FESdevice2024/Functional_Electronic_Stimulation/FES Paper Images/Figure 5 Fab.png

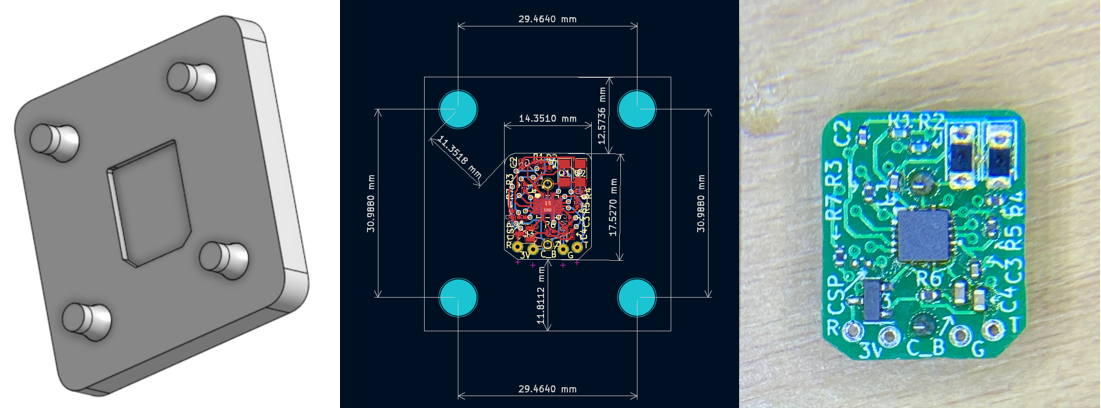
FES Paper Images/Figure 5 Fab.png
