FESdevice2024/Functional_Electronic_Stimulation/FES Paper Images/Figure 3 Battery Discharging For Clock.png

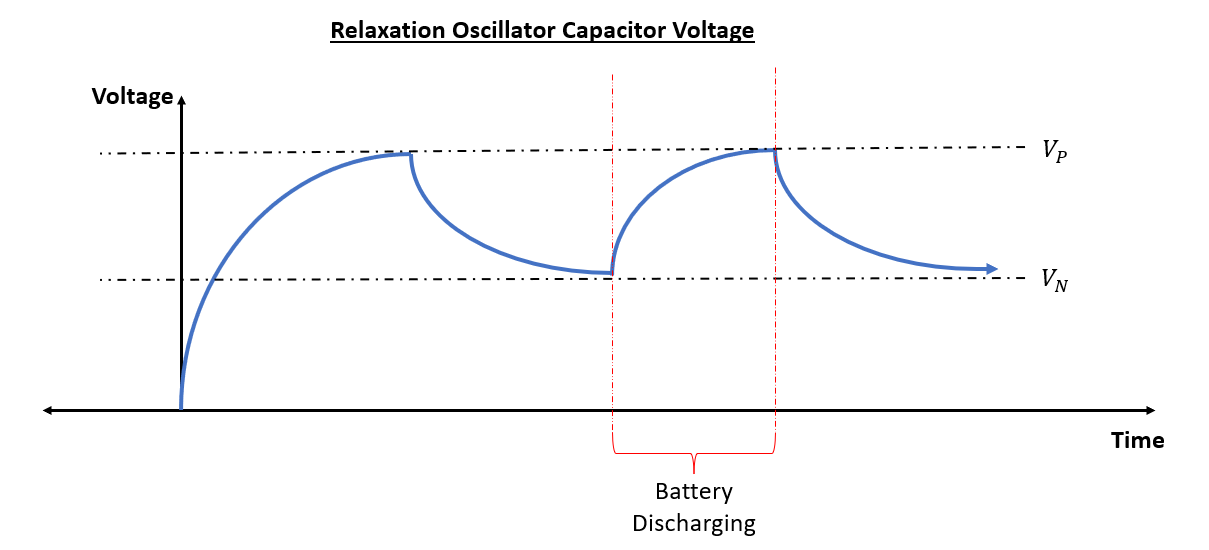
FES Paper Images/Figure 3 Battery Discharging For Clock.png
