FESdevice2024/Functional_Electronic_Stimulation/FES Paper Images/Figure 3 Cap Charging for Batt Life Calcs.png

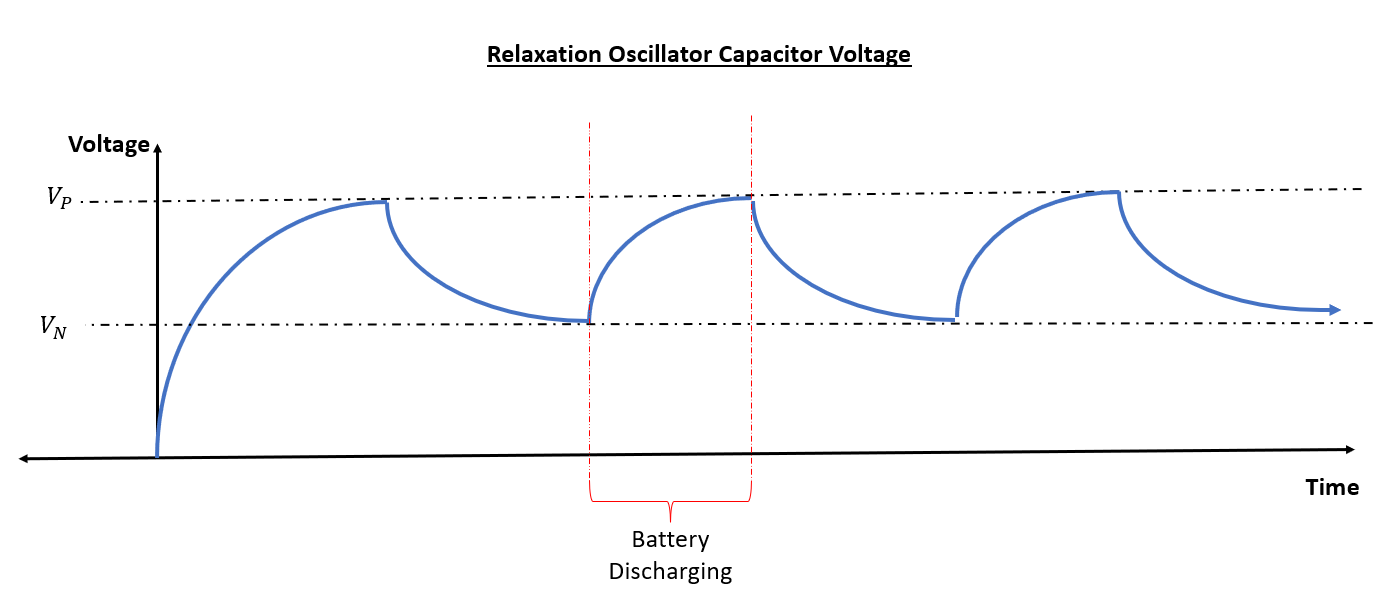
FES Paper Images/Figure 3 Cap Charging for Batt Life Calcs.png
