FESdevice2024/Functional_Electronic_Stimulation/FES Paper Images/Figure 7 Meas Hz.png

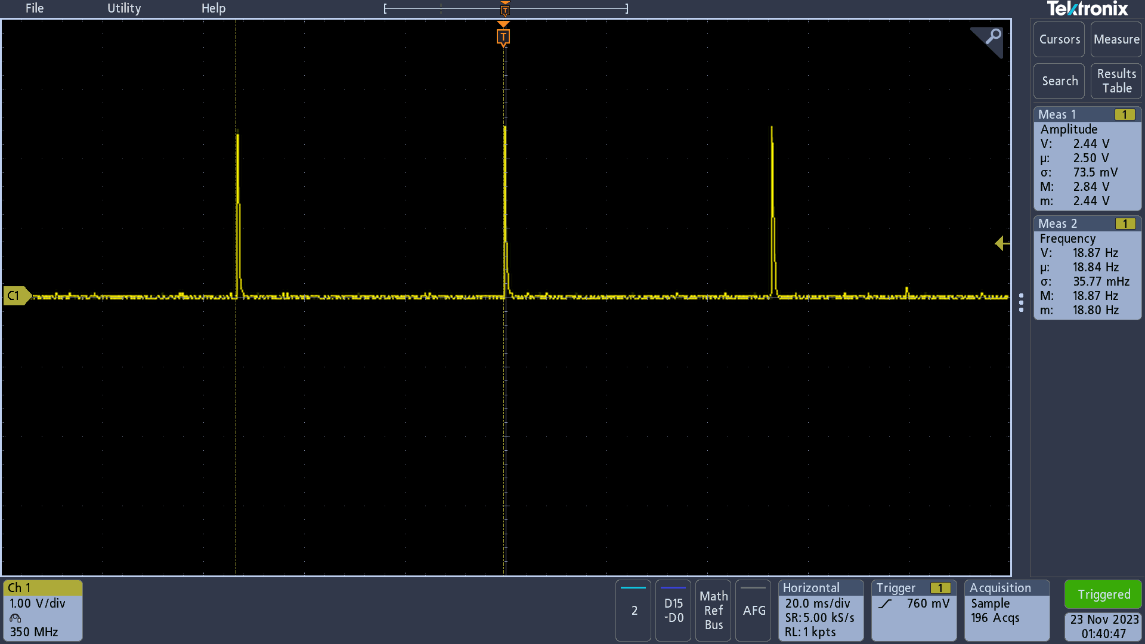
FES Paper Images/Figure 7 Meas Hz.png
