FESdevice2024/Functional_Electronic_Stimulation/FES Paper Images/Figure 8 Pulse Width.png

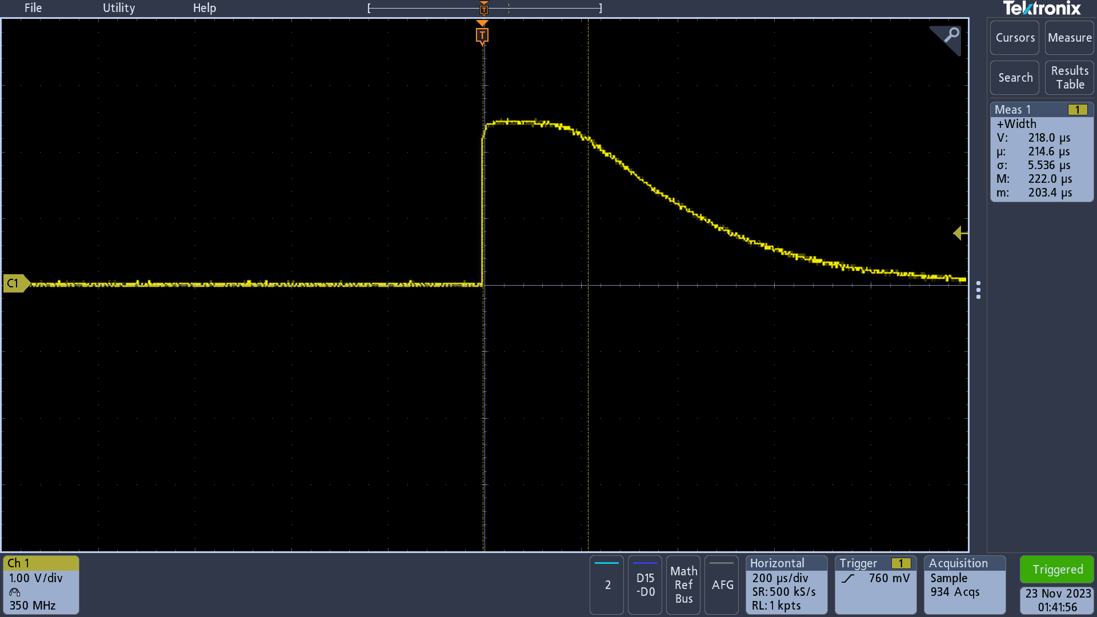
FES Paper Images/Figure 8 Pulse Width.png
