FESdevice2024/Functional_Electronic_Stimulation/FES Paper Images/Salmons Original Circuit Figure 1.jpg

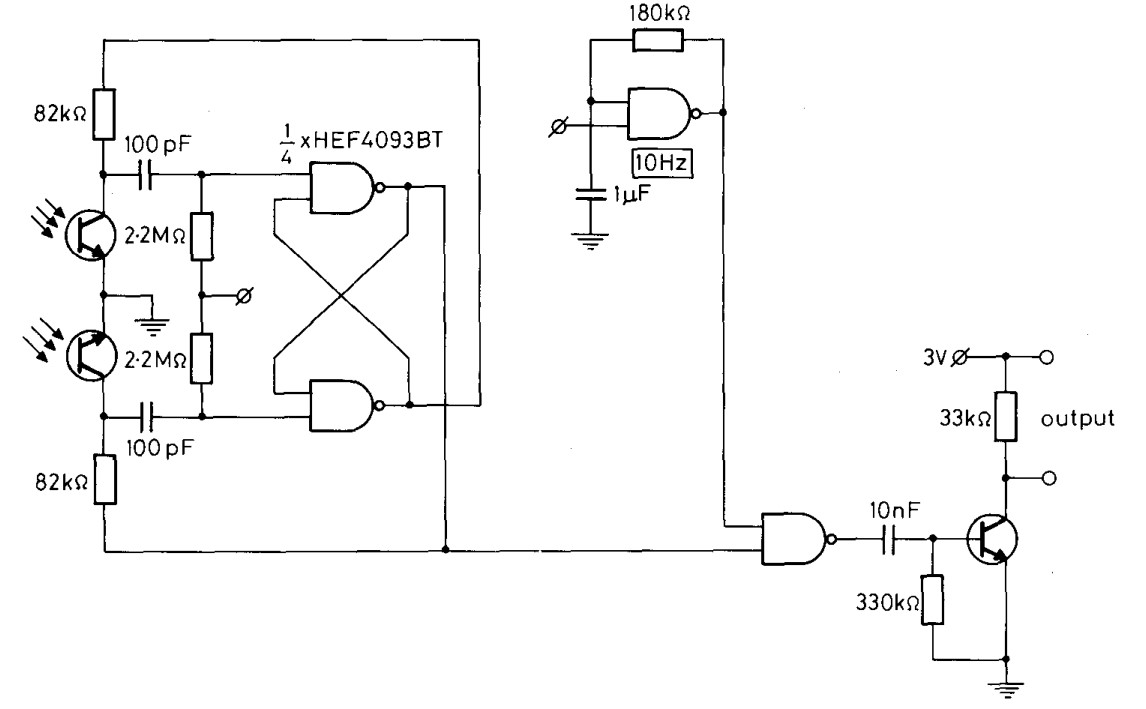
FES Paper Images/Salmons Original Circuit Figure 1.jpg
