FESdevice2024/Functional_Electronic_Stimulation/FES Oscilloscope Images From Testing/clock1.png

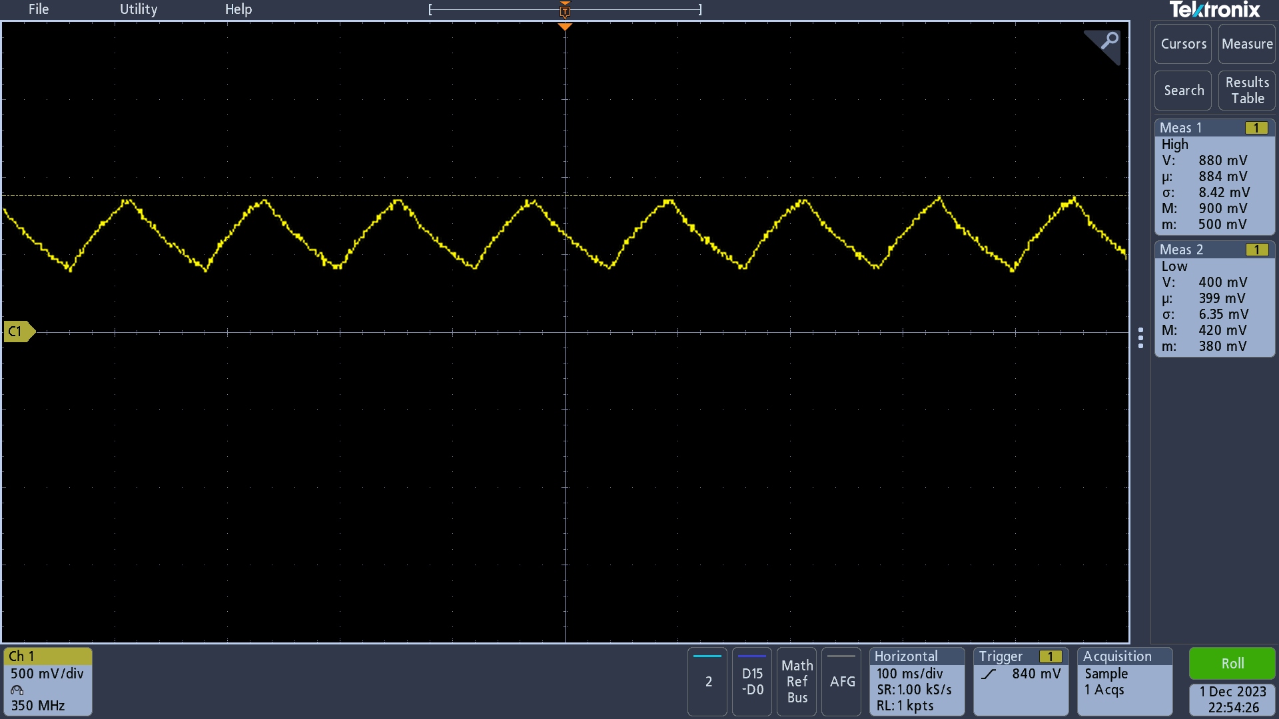
FES Oscilloscope Images From Testing/clock1.png
