FESdevice2024/Functional_Electronic_Stimulation/FES Oscilloscope Images From Testing/clock5.png

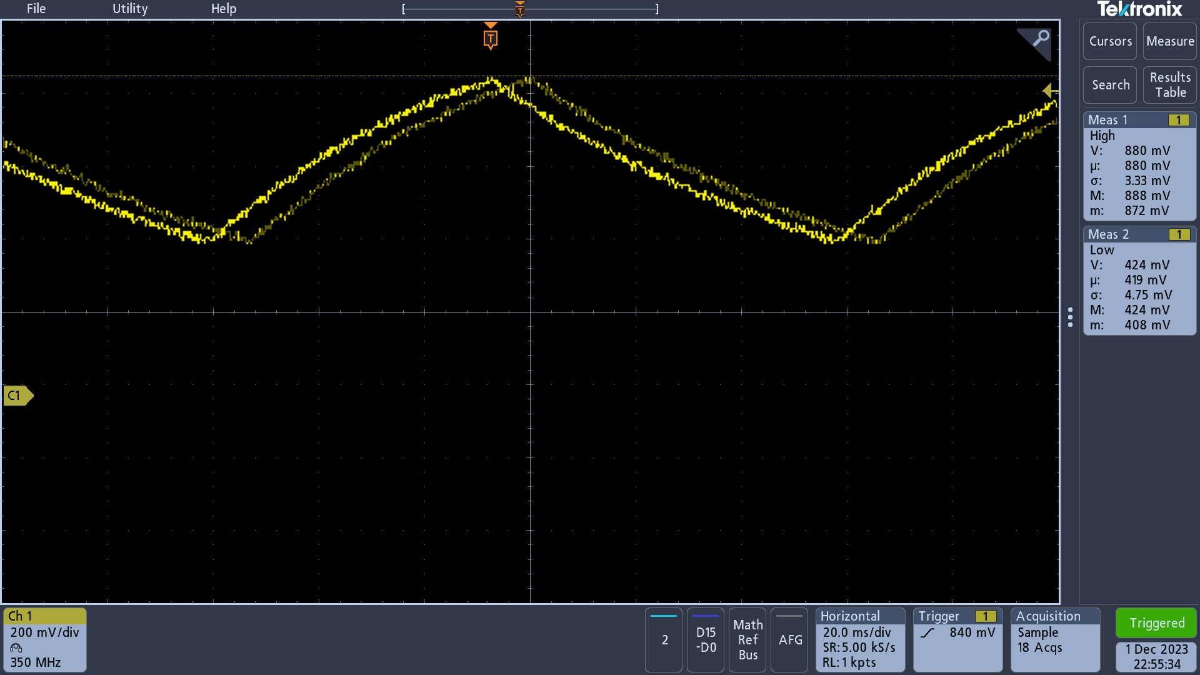
FES Oscilloscope Images From Testing/clock5.png
