FESdevice2024/Functional_Electronic_Stimulation/FES Oscilloscope Images From Testing/clock7.png

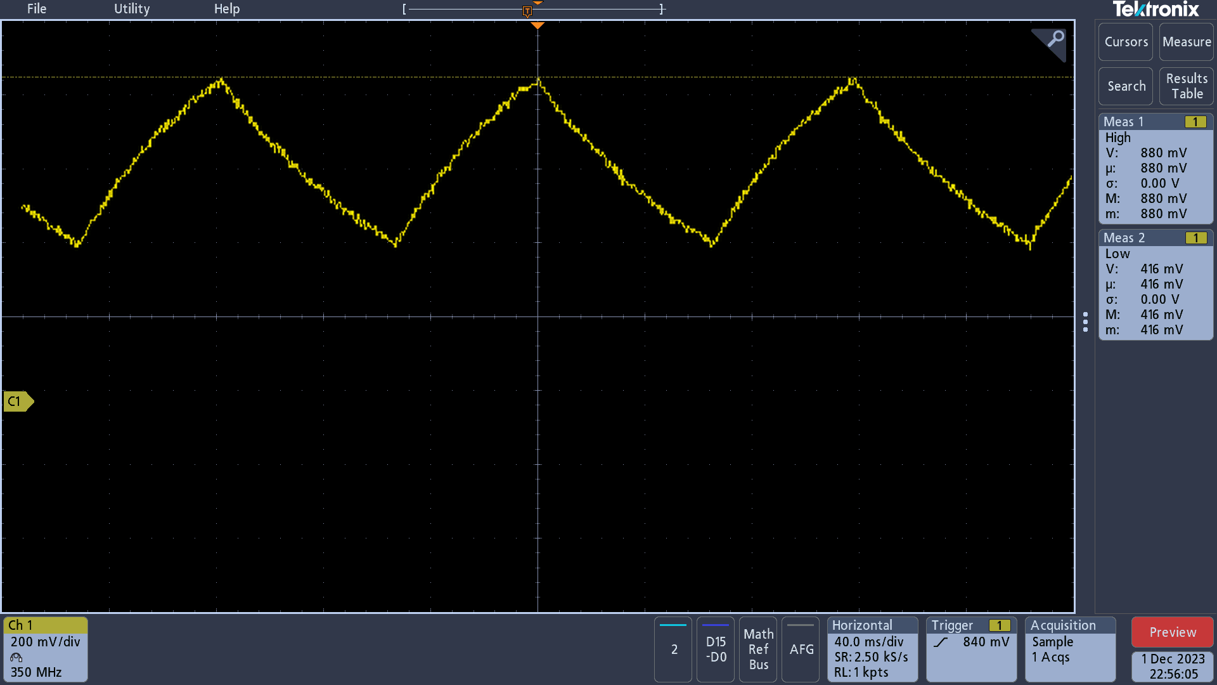
FES Oscilloscope Images From Testing/clock7.png
