FESdevice2024/Functional_Electronic_Stimulation/FES Oscilloscope Images From Testing/Figure 6.png

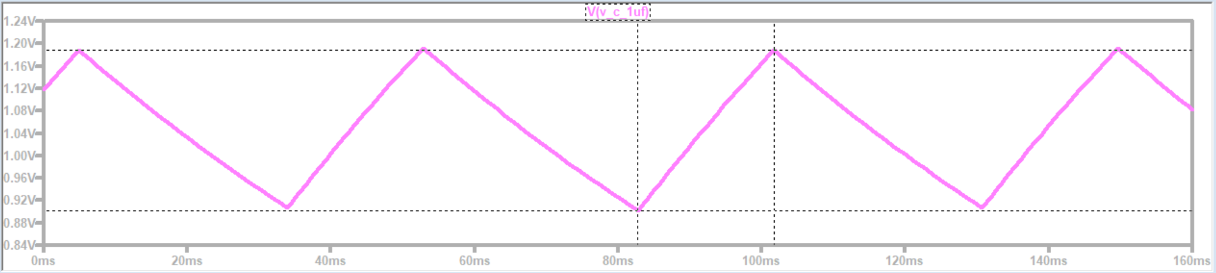
FES Oscilloscope Images From Testing/Figure 6.png
