FESdevice2024/Functional_Electronic_Stimulation/FES Oscilloscope Images From Testing/New Figure 7 Pulse.png

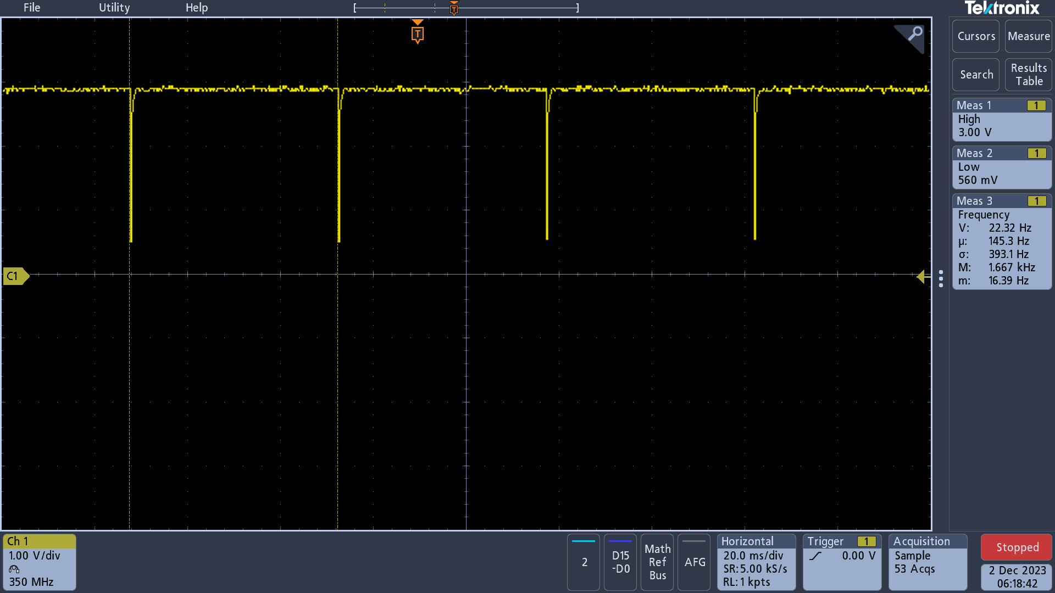
FES Oscilloscope Images From Testing/New Figure 7 Pulse.png
