FESdevice2024/Functional_Electronic_Stimulation/FES Oscilloscope Images From Testing/tek00001.png

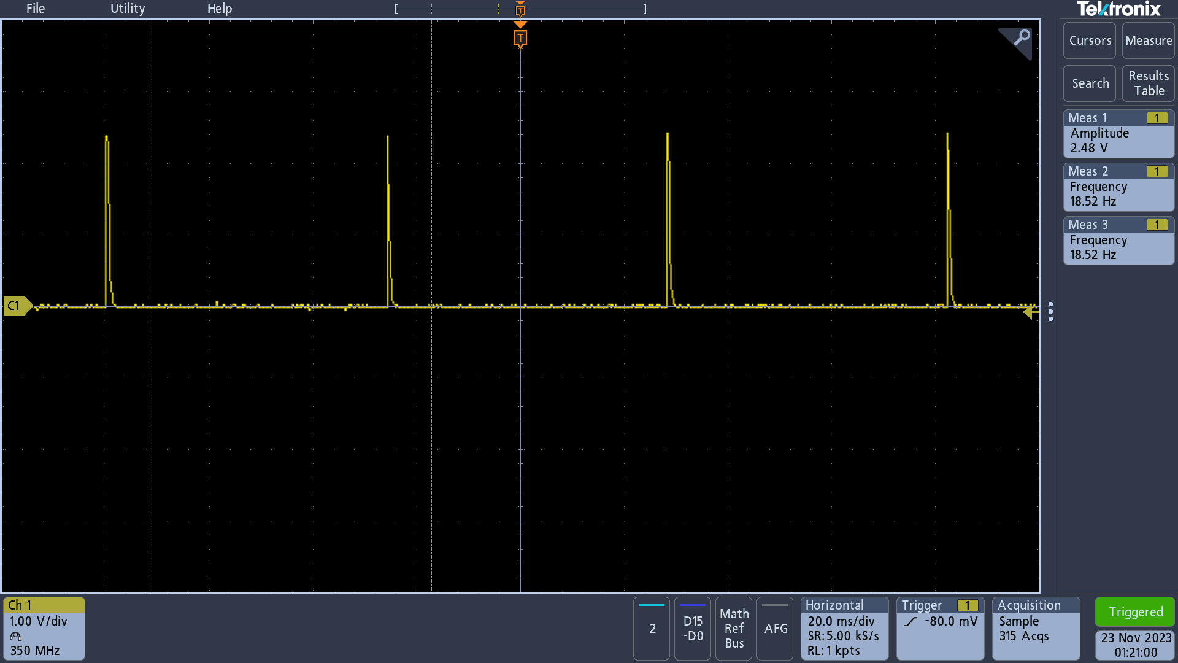
FES Oscilloscope Images From Testing/tek00001.png
