FESdevice2024/Functional_Electronic_Stimulation/FES Oscilloscope Images From Testing/Untitled Images/3vc4.png

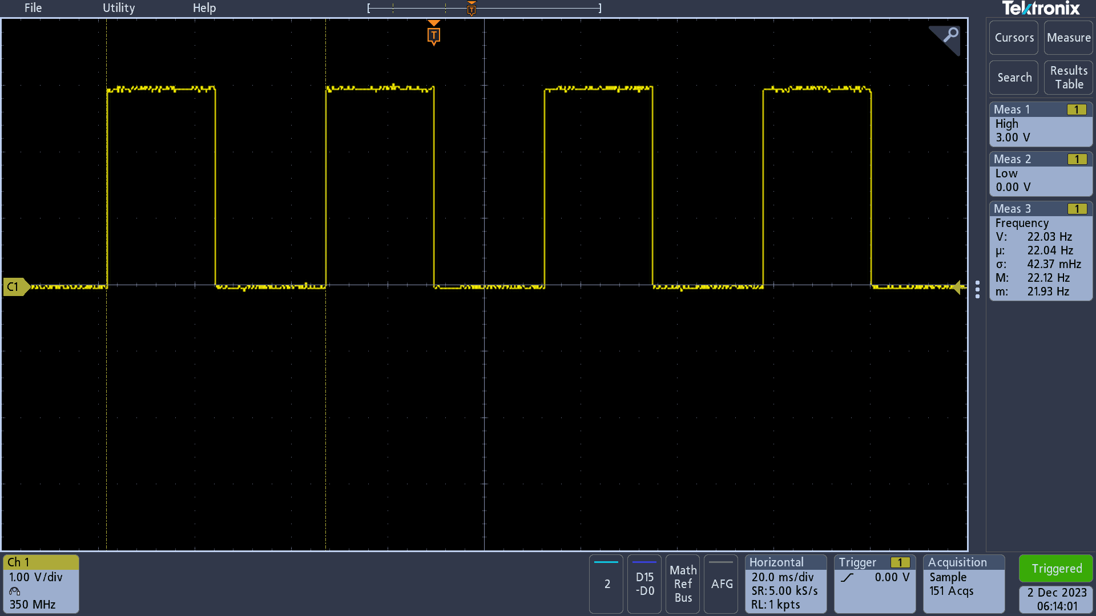
FES Oscilloscope Images From Testing/Untitled Images/3vc4.png
