FESdevice2024/Functional_Electronic_Stimulation/FES Oscilloscope Images From Testing/Untitled Images/tek00008.png

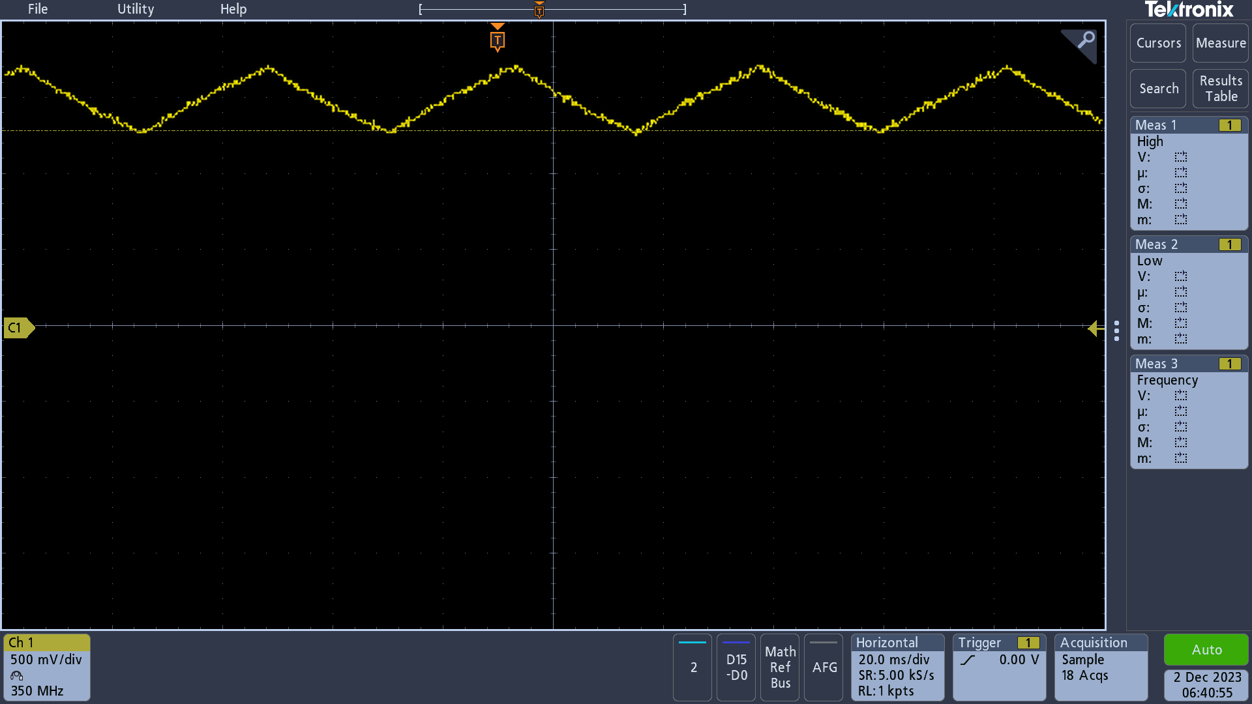
FES Oscilloscope Images From Testing/Untitled Images/tek00008.png
