FESdevice2024/Functional_Electronic_Stimulation/FES LTSpice Simulations/FES Clock Generation and Control.asc

C1: cap; 1µ
R1: res; 120k
U1: SN74AHC132
V1: voltage; PWL(0 3 1 3 1.0001 0)
V2: voltage; 3
Named nets: 0, Vout, Vcc, Vcontrol, V_C_1uF
.tran 0 1 0.5
