FESdevice2024/Functional_Electronic_Stimulation/FES LTSpice Simulations/FES Output Sim.asc

C1: cap; 10n
C2: cap; 1µ
Q1: npn; ZTX1048A
R1: res; 330k
R2: res; 33k
R3: res; 1k
R4: res; 120k
U1: SN74AHC132
U2: SN74AHC132
V2: voltage; 3
V5: voltage; PULSE(0 3 0.5 10n 10n 3 4)
Named nets: 0, Vcc, Vout, Von_off, Vcheck, Vclock
.tran 0 200.4m 199.9m
.tran 0 1 0
